joba-1/UselessBox/kicad/UselessBox.sch

## KiCad design kicad/UselessBox.sch (2021-04-08)

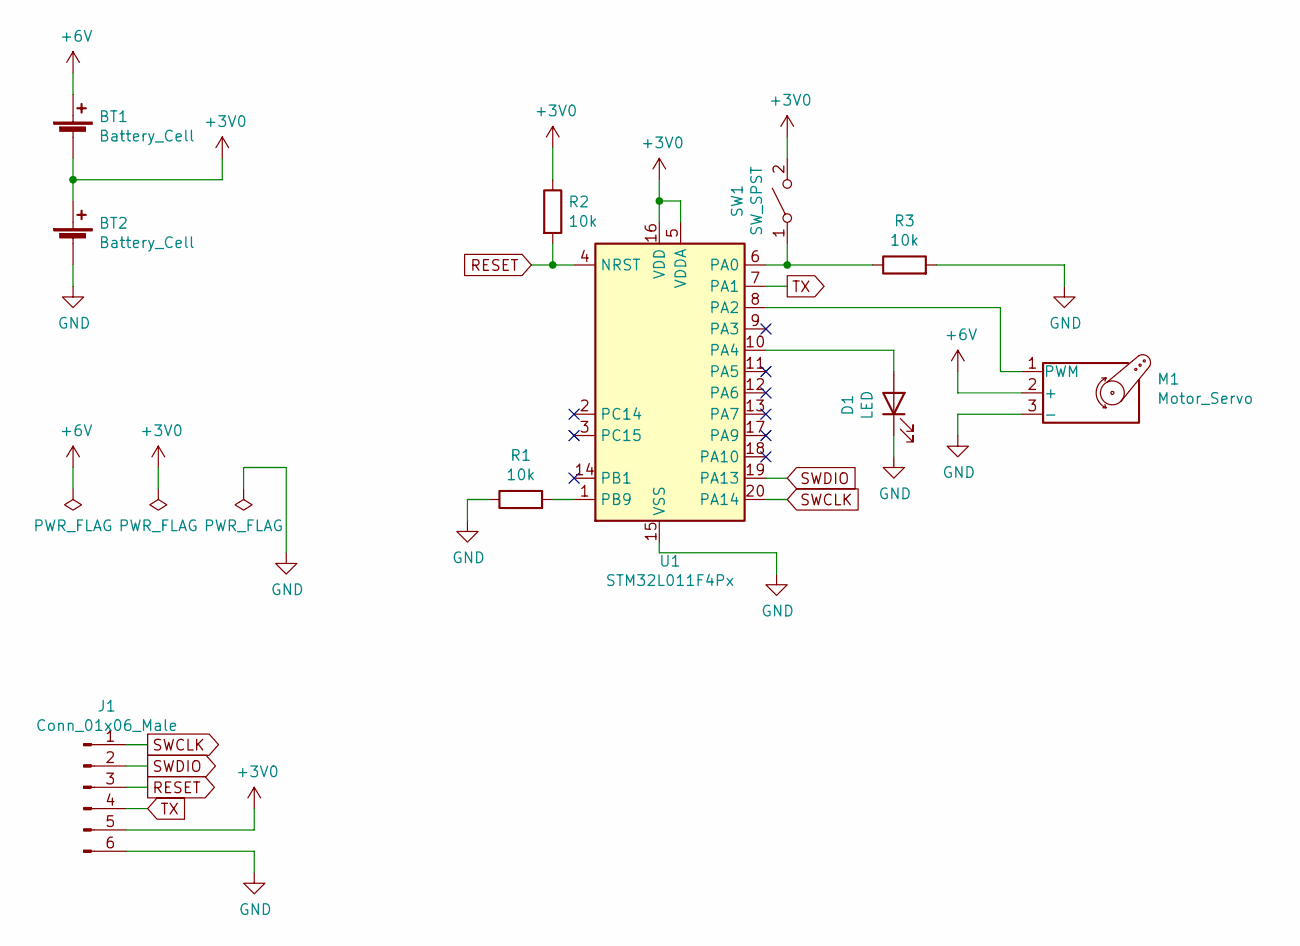
[picture p6: schematic UselessBox.sch]

Parts:
BT1, BT2: Battery_Cell
D1: LED
J1: Conn_01x06_Male
M1: Motor_Servo
R1, R2, R3: 10k
SW1: SW_SPST
U1: STM32L011F4Px; TSSOP-20_4.4x6.5mm_P0.65mm

Connections:
+3V0: BT1.2 (-), BT2.1 (+), J1.5, R2.1, SW1.2 (B), U1.5 (VDDA), U1.16 (VDD)
+6V: BT1.1 (+), M1.2 (+)
GND: BT2.2 (-), D1.1 (K), J1.6, M1.3 (-), R1.1, R3.2, U1.15 (VSS)
unnamed: D1.2 (A), U1.10 (PA4)
unnamed: M1.1 (PWM), U1.8 (PA2)
unnamed: R1.2, U1.1 (PB9)
unnamed: R3.1, SW1.1 (A), U1.6 (PA0)
RESET: J1.3, R2.2, U1.4 (NRST)
SWCLK: J1.1, U1.20 (PA14)
SWDIO: J1.2, U1.19 (PA13)
TX: J1.4, U1.7 (PA1)
